mox-mox/solar/vreg5.pdf

## WEBENCH ® Design Report

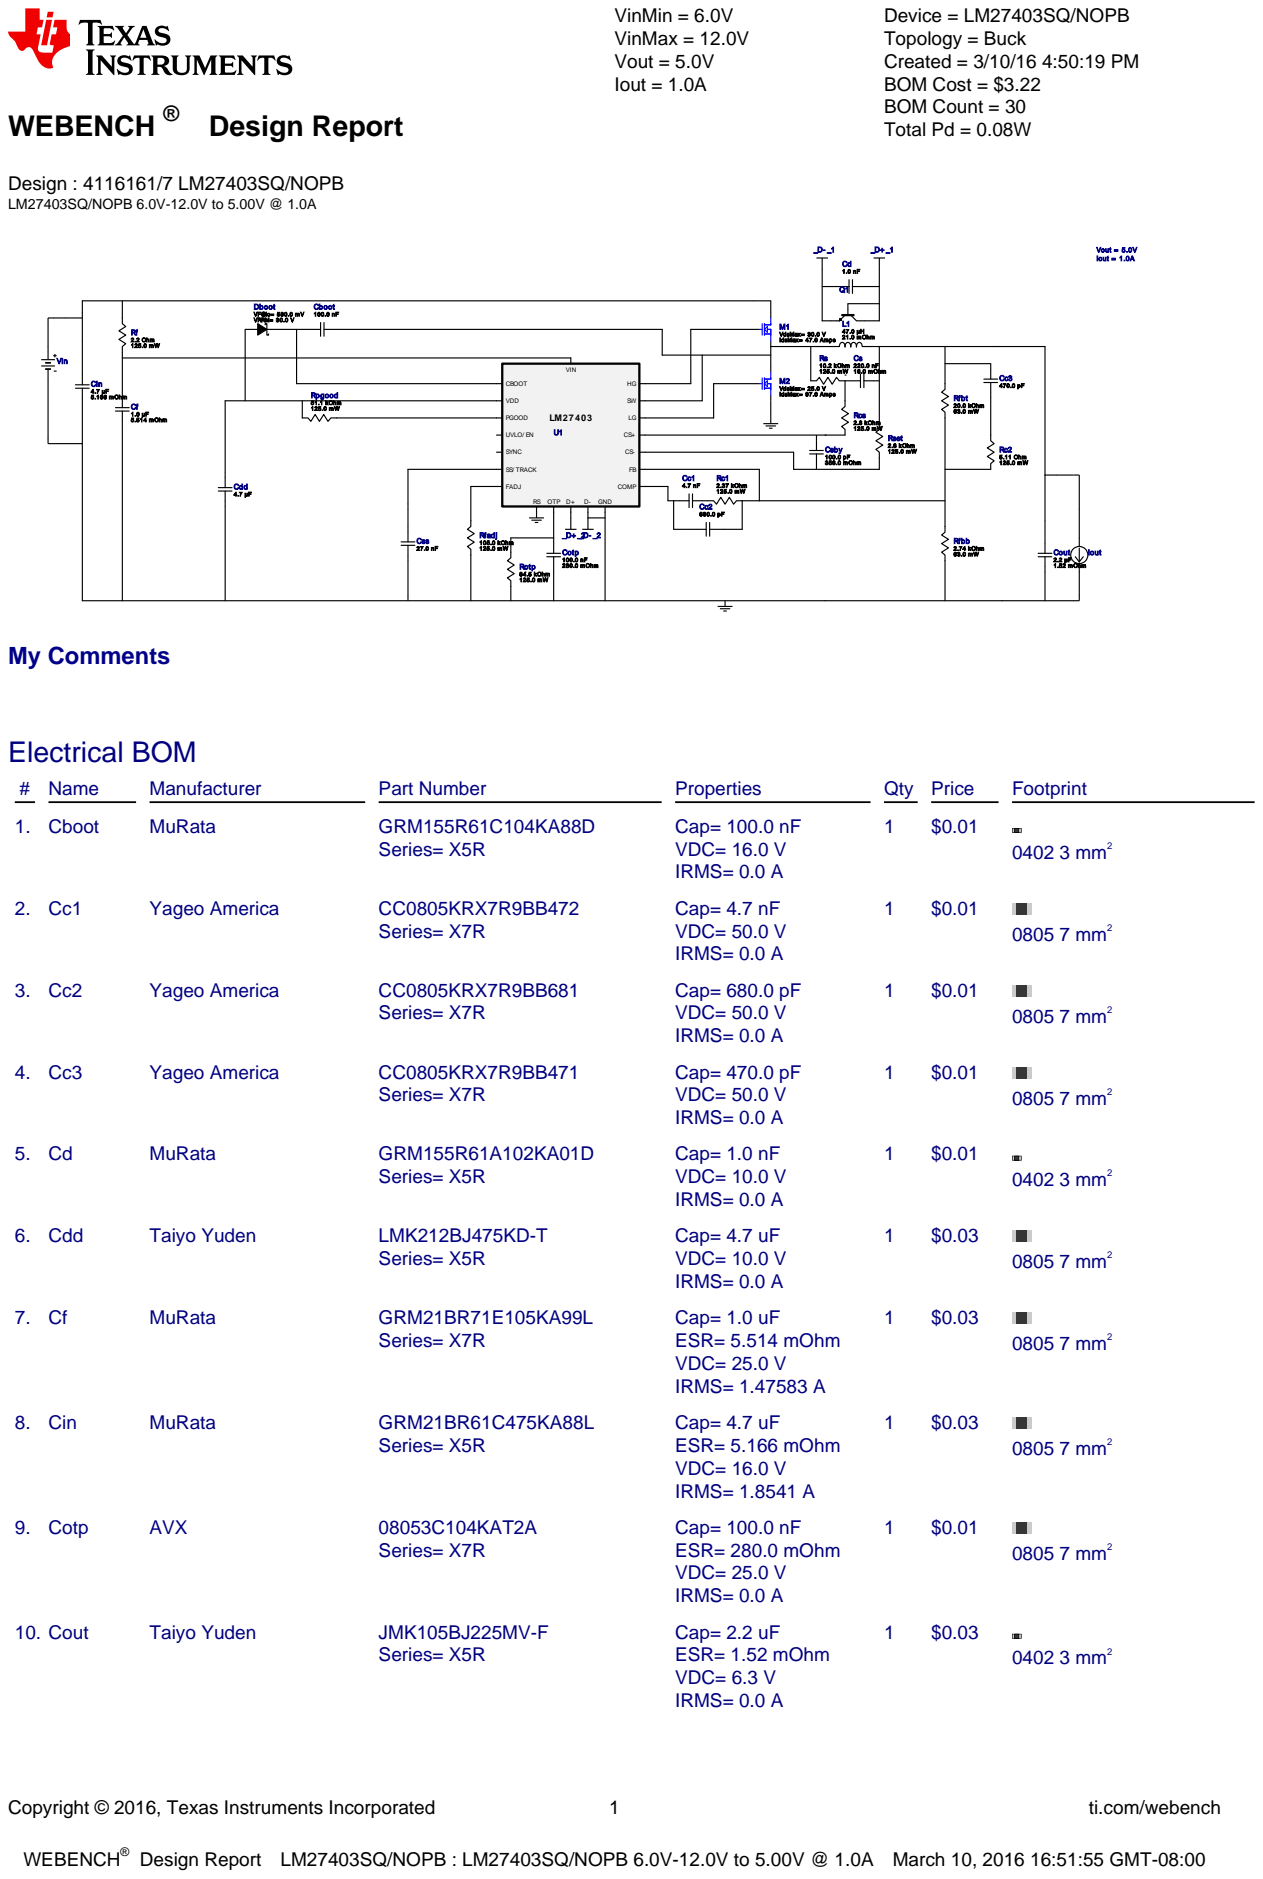
[picture p56: page 1]
Copyright © 2016, Texas Instruments Incorporated; ti.com/webench; WEBENCH®; Design : 4116161/7 LM27403SQ/NOPB LM27403SQ/NOPB 6.0V-12.0V to 5.00V @ 1.0A; VinMin = 6.0V VinMax = 12.0V Vout = 5.0V Iout = 1.0A; Device = LM27403SQ/NOPB Topology = Buck Created = 3/10/16 4:50:19 PM BOM Cost = $3.22 BOM Count = 30 Total Pd = 0.08W; Cboot 100.0 nF; Cdd 4.7 µF; 5.514 mOhm; Cin 4.7 µF 5.166 mOhm; Cotp 100.0 nF 280.0 mOhm; Cout 2.2 µF; 1.52 mOhm; Cs 220.0 nF 16.0 mOhm; Csby 100.0 pF 356.0 mOhm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

Dboot VF@Io= 580.0 mV

Design Report LM27403SQ/NOPB : LM27403SQ/NOPB 6.0V-12.0V to 5.00V @ 1.0A March 10, 2016 16:51:55 GMT-08:00

Design

Copyright © 2016, Texas Instruments Incorporated | 2 | ti.com/webench
# Name | Manufacturer | Part Number | Properties | Qty Price | Footprint

11. Cs | AVX | 0805YC224KAT2A (http://www.avx.com/docs/masterpubs/smccp.pdf) Series= X7R | Cap= 220.0 nF ESR= 16.0 mOhm VDC= 16.0 V IRMS= 0.0 A
1 | $0.03
| | | | | 0805 7 mm²
12. Csby | AVX | 08055A101JAT2A (http://www.avx.com/docs/masterpubs/smccp.pdf) Series= C0G/NP0

Cap= 100.0 pF
ESR= 356.0 mOhm
VDC= 50.0 V
IRMS= 0.0 A

1 $0.01
0805 7 mm²
13. Css | MuRata | GRM155R61C273KA01D (http://search.murata.co.jp/Ceramy/PnsearchViewAction.do) Series= X5R | Cap= 27.0 nF VDC= 16.0 V IRMS= 0.0 A
1 | $0.01
0402 3 mm²
14. Dboot | Diodes Inc. | SBR0230T5-7-F (http://www.diodes.com/datasheets/sbr/SBR0230T5.pdf) | VF@Io= 580.0 mV VRRM= 30.0 V
1 | $0.10
SOD-523 5 mm²
15. L1 | Coilcraft | SER1390-473MLB (http://www.coilcraft.com/pdfs/ser1390.pdf) | L= 47.0 µH DCR= 21.0 mOhm
1 | $0.95

SER1390 240 mm²
16. M1 | Texas Instruments | CSD17308Q3 (http://www.ti.com/lit/ds/symlink/csd17308q3.pdf) | VdsMax= 30.0 V IdsMax= 47.0 Amps | 1 | $0.34

TRANS_NexFET_Q3 18
mm²
17. M2 | Texas Instruments | CSD16322Q5C (http://focus.ti.com/lit/ds/symlink/csd16322q5c.pdf) | VdsMax= 25.0 V IdsMax= 97.0 Amps | 1 | $0.50

TRANS_NexFET_Q5C 56
mm²
18. Q1 | Diodes Inc. | MMBT3904T (http://www.diodes.com/datasheets/ds30270.pdf) | Bipolar Transistor | 1 | $0.04
SOT-523 7 mm²
19. Rc1 | Panasonic | ERJ-6ENF2371V (http://www.panasonic.com/industrial/components/pdf/AOA0000CE2.pdf) Series= ERJ-6E | Res= 2.37 kOhm Power= 125.0 mW Tolerance= 1.0% | 1 | $0.01
0805 7 mm²
20. Rc2 | Vishay-Dale | CRCW08055R11FKEA (http://www.vishay.com/docs/20035/dcrcwe3.pdf) Series= CRCW..e3 | Res= 5.11 Ohm Power= 125.0 mW Tolerance= 1.0% | 1 | $0.01
0805 7 mm²
21. Rcs | Panasonic | ERJ-6ENF2801V (http://www.panasonic.com/industrial/components/pdf/AOA0000CE2.pdf) Series= ERJ-6E | Res= 2.8 kOhm Power= 125.0 mW Tolerance= 1.0% | 1 | $0.01
0805 7 mm²
22. Rf | Yageo America | RC0805FR-072R2L (http://www.yageo.com/documents/recent/PYu%2DRC0805%5F51%5FRoHS%5FL%5F6.pdf) Series= ? | Res= 2.2 Ohm Power= 125.0 mW Tolerance= 1.0% | 1 | $0.01
0805 7 mm²
23. Rfadj | Panasonic | ERJ-6ENF1053V (http://www.panasonic.com/industrial/components/pdf/AOA0000CE2.pdf) Series= ERJ-6E | Res= 105.0 kOhm Power= 125.0 mW Tolerance= 1.0% | 1 | $0.01
0805 7 mm²
24. Rfbb | Vishay-Dale | CRCW04022K74FKED (http://www.vishay.com/docs/20035/dcrcwe3.pdf) Series= CRCW..e3 | Res= 2.74 kOhm Power= 63.0 mW Tolerance= 1.0% | 1 | $0.01
0402 3 mm²
25. Rfbt | Vishay-Dale | CRCW040220K0FKED (http://www.vishay.com/docs/20035/dcrcwe3.pdf) Series= CRCW..e3 | Res= 20.0 kOhm Power= 63.0 mW Tolerance= 1.0% | 1 | $0.01
0402 3 mm²
26. Rotp | Panasonic | ERJ-6ENF8452V (http://www.panasonic.com/industrial/components/pdf/AOA0000CE2.pdf) Series= ERJ-6E | Res= 84.5 kOhm Power= 125.0 mW Tolerance= 1.0% | 1 | $0.01
0805 7 mm²
27. Rpgood | Panasonic | ERJ-6ENF5112V (http://www.panasonic.com/industrial/components/pdf/AOA0000CE2.pdf) Series= ERJ-6E | Res= 51.1 kOhm Power= 125.0 mW Tolerance= 1.0% | 1 | $0.01
0805 7 mm²
28. Rs | Panasonic | ERJ-6ENF1022V (http://www.panasonic.com/industrial/components/pdf/AOA0000CE2.pdf) Series= ERJ-6E | Res= 10.2 kOhm Power= 125.0 mW Tolerance= 1.0% | 1 | $0.01
0805 7 mm²

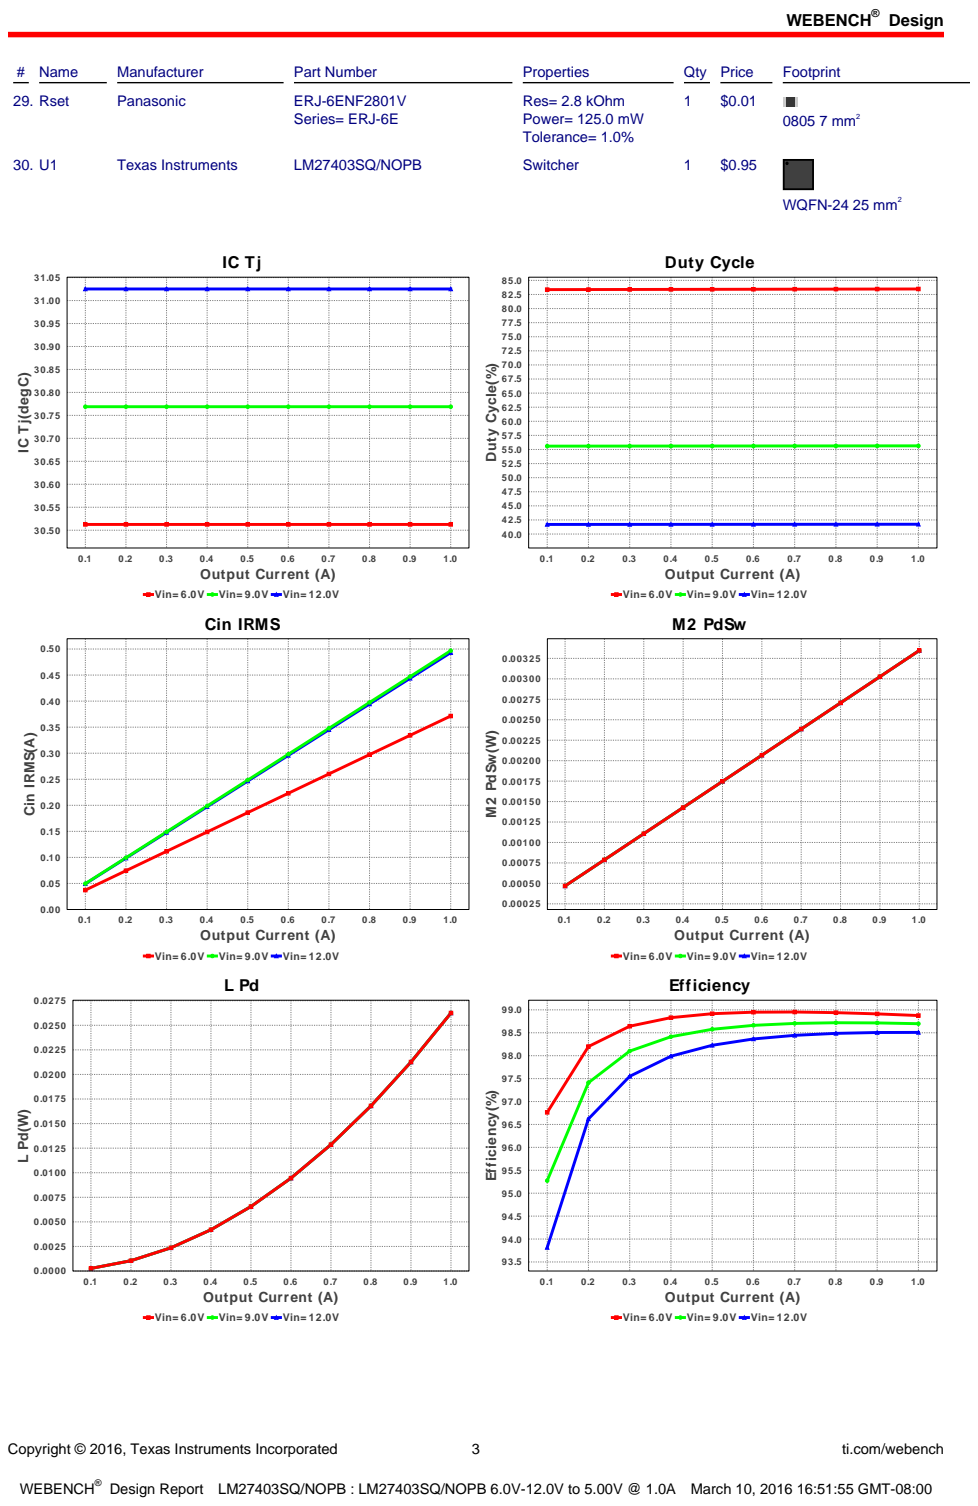
[picture p57: page 3]
Copyright © 2016, Texas Instruments Incorporated; ti.com/webench; # Name; Manufacturer; Part Number; Properties; Qty Price; Footprint; 29. Rset; Panasonic; ERJ-6ENF2801V; Series= ERJ-6E; Res= 2.8 kOhm Power= 125.0 mW Tolerance= 1.0%; 0805 7 mm²; Texas Instruments; LM27403SQ/NOPB; Switcher; WQFN-24 25 mm²; 1.0 Output Current (A); Duty Cycle; Duty Cycle(%); Cin IRMS(A); M2 PdSw(W); Efficiency(%)

IC Tj(degC)

Vin= 6.0V Vin= 9.0V Vin= 12.0V
Cin IRMS

M2 PdSw

Efficiency

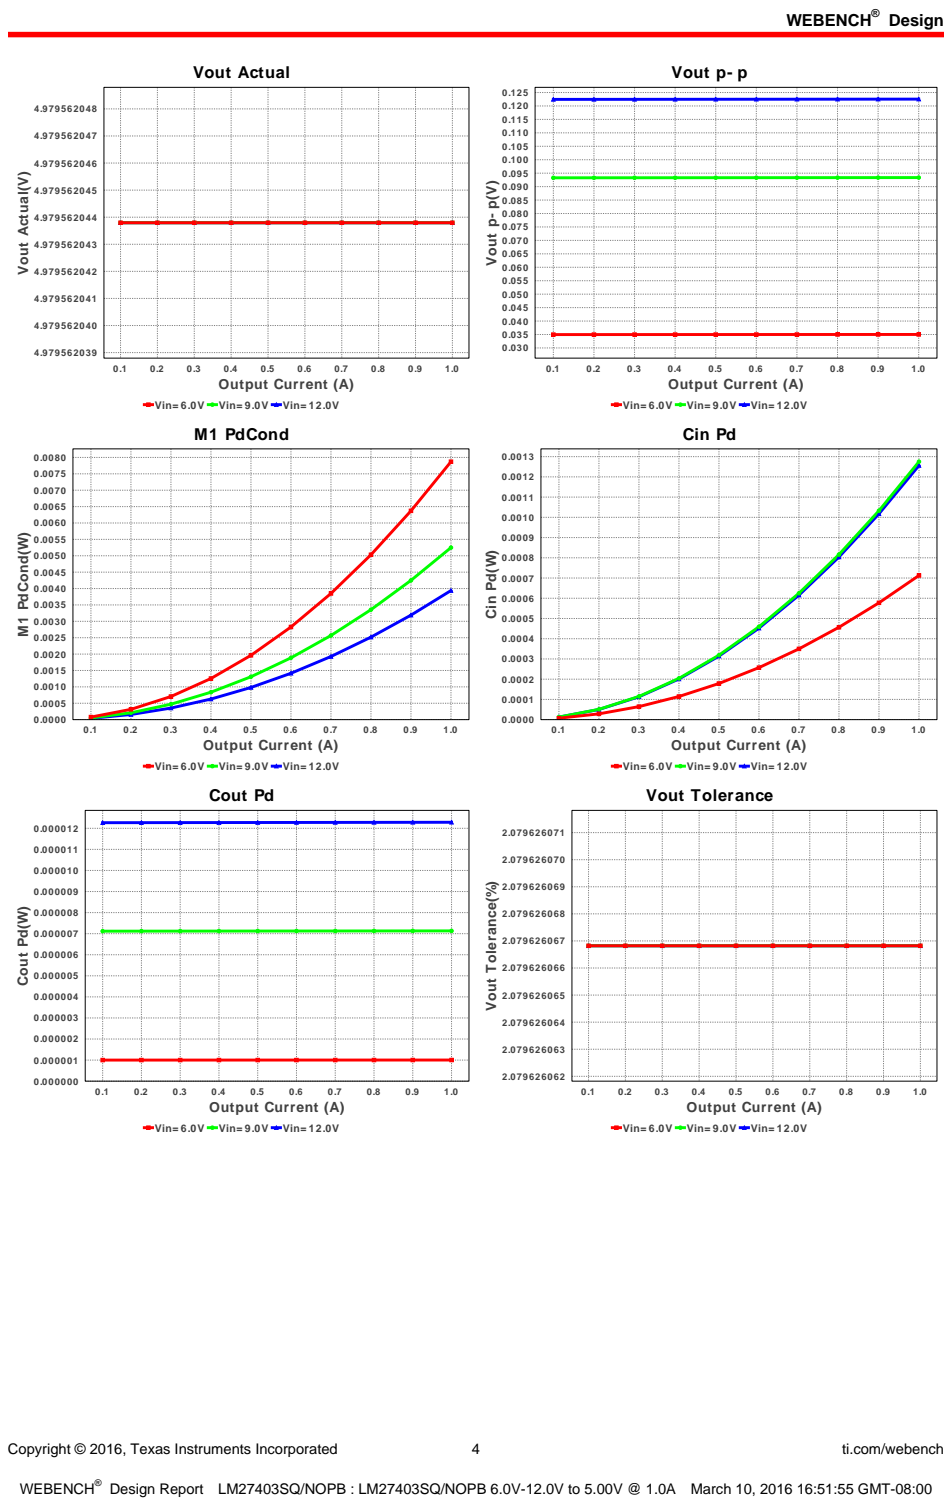
[picture p58: page 4]
Copyright © 2016, Texas Instruments Incorporated; ti.com/webench; Vout Actual; 1.0 Output Current (A); Vout Actual(V); Vout p- p; Vout p- p(V); M1 PdCond(W); Cin Pd; Cin Pd(W); Cout Pd(W); Vout Tolerance(%)

Vin= 6.0V Vin= 9.0V Vin= 12.0V
M1 PdCond

Cout Pd

Vout Tolerance

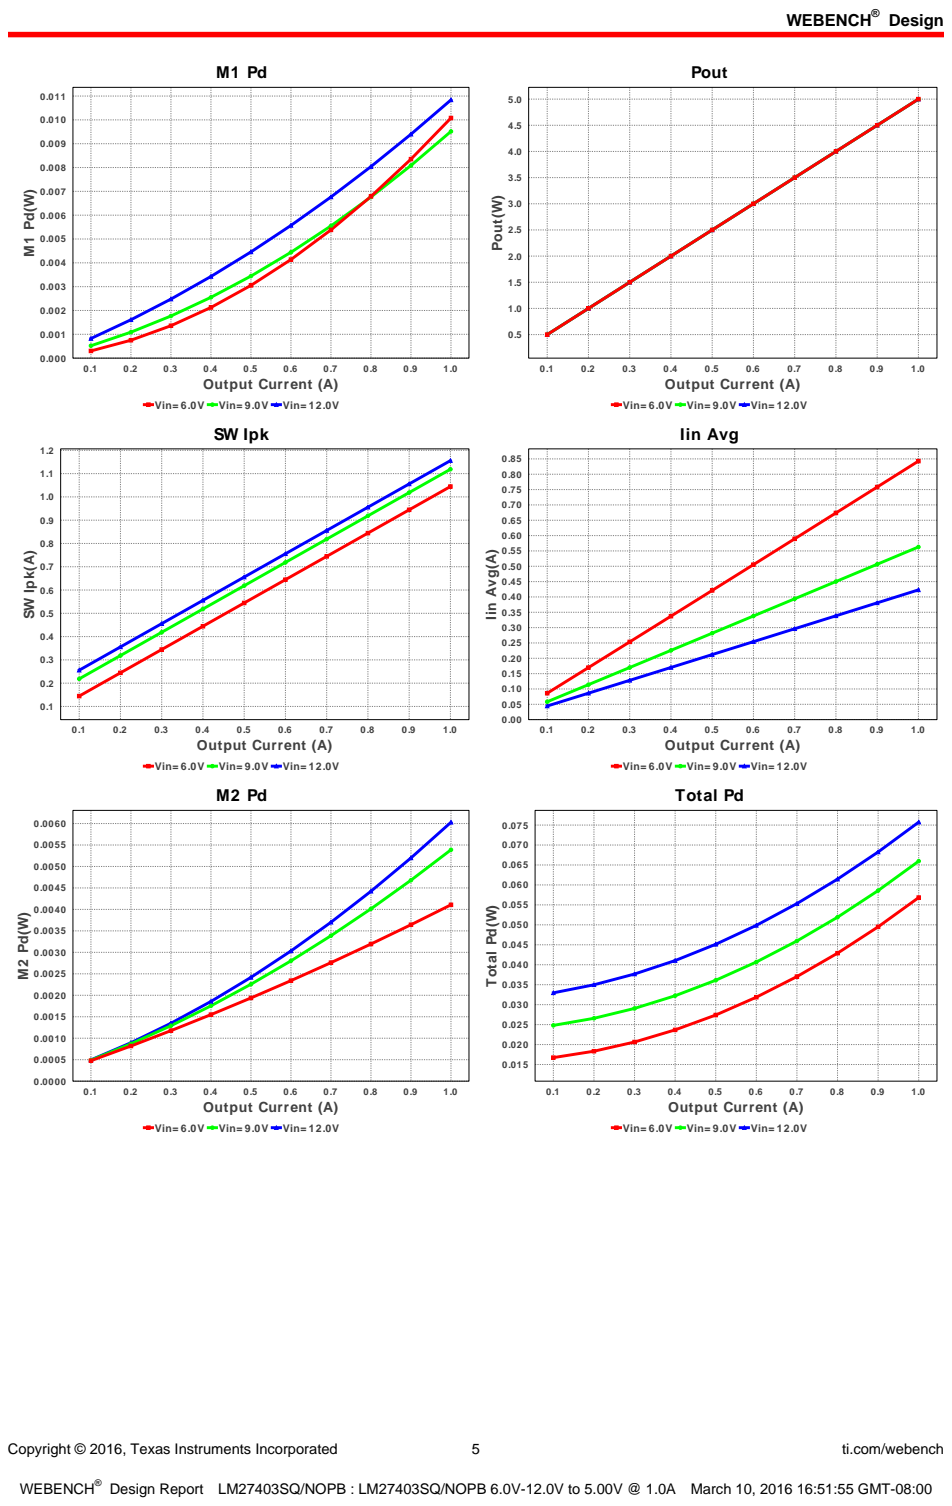
[picture p59: page 5]
Copyright © 2016, Texas Instruments Incorporated; ti.com/webench; 1.0 Output Current (A); Pout; Pout(W); SW Ipk; SW Ipk(A); Iin Avg(A); Total Pd(W)

Vin= 6.0V Vin= 9.0V Vin= 12.0V

Iin Avg

Total Pd

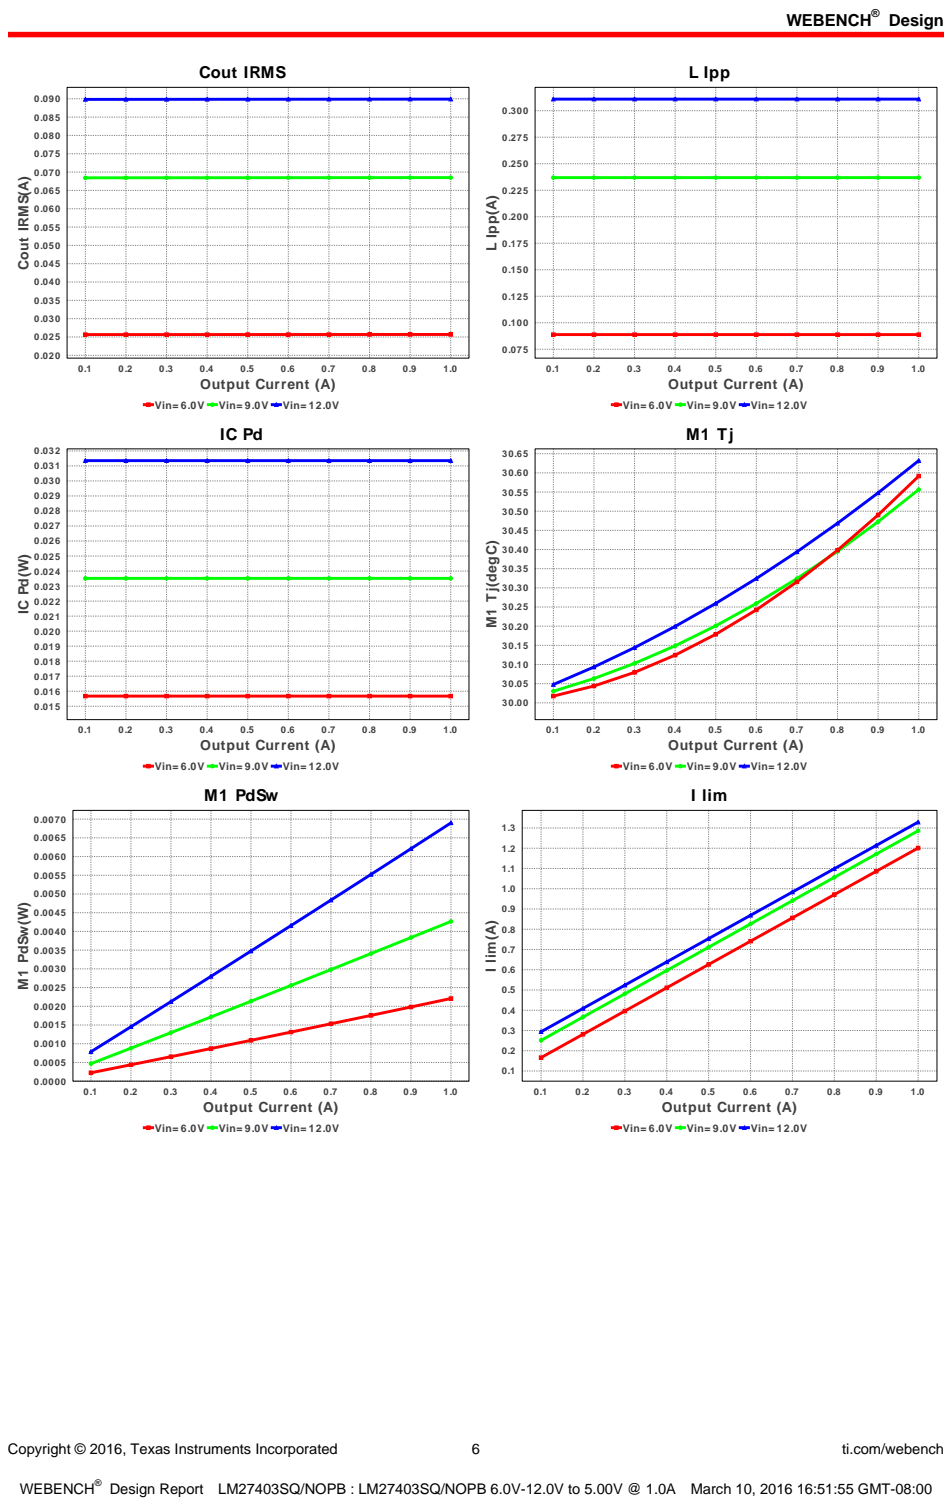
[picture p60: page 6]
Copyright © 2016, Texas Instruments Incorporated; ti.com/webench; Cout IRMS; 1.0 Output Current (A); Cout IRMS(A); L Ipp; L Ipp(A); M1 Tj(degC); M1 PdSw(W); I lim; I lim(A)

Vin= 6.0V Vin= 9.0V Vin= 12.0V

M1 PdSw

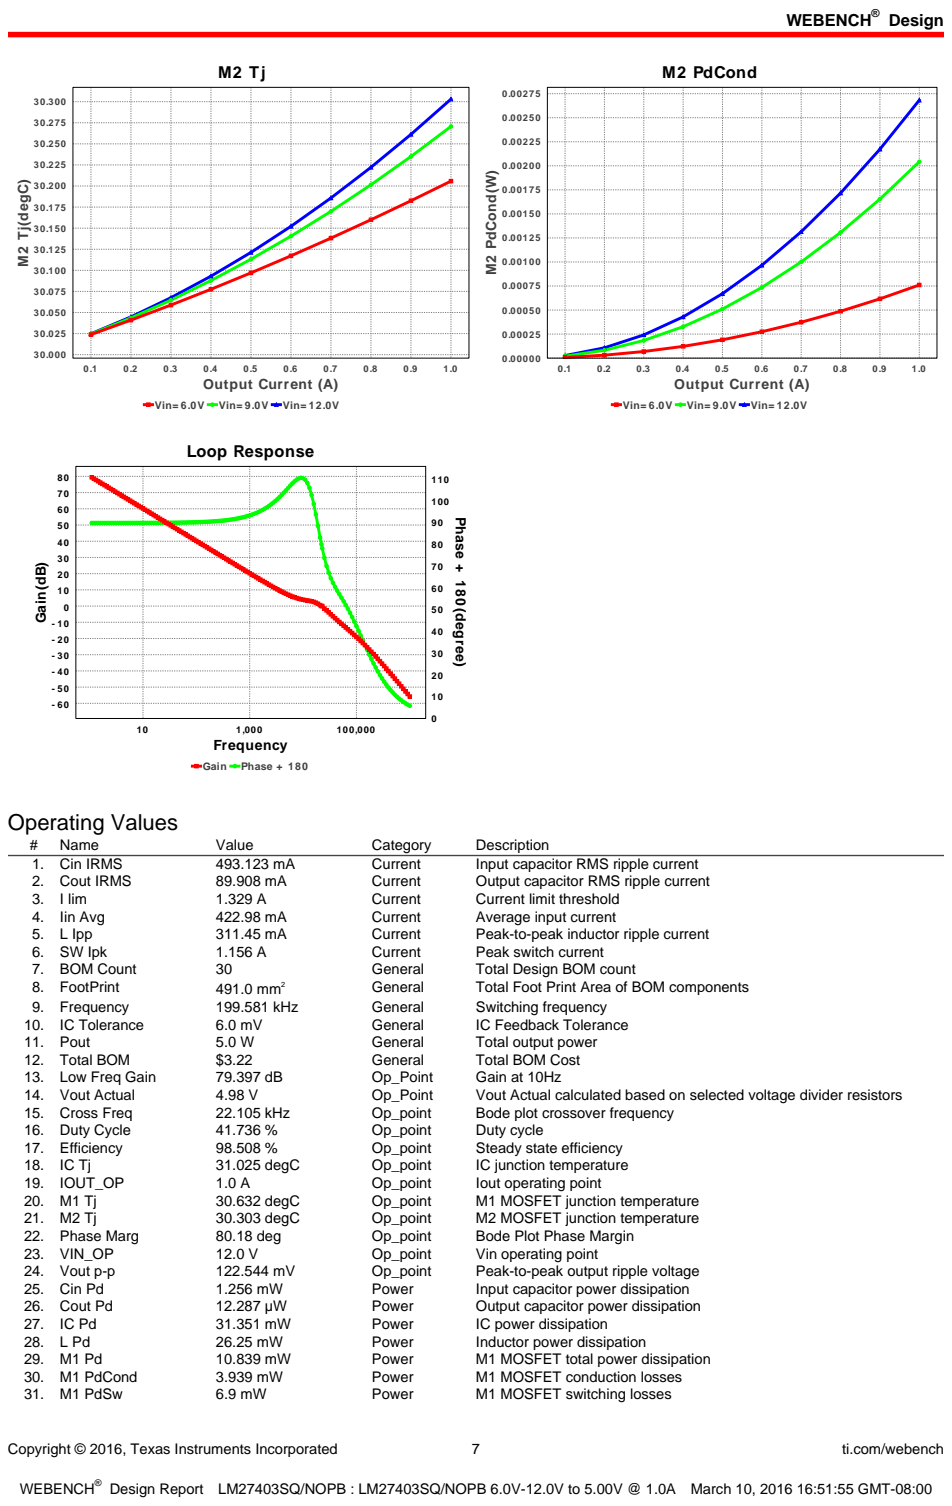
[picture p61: page 7]
Copyright © 2016, Texas Instruments Incorporated; ti.com/webench; 1.0 Output Current (A); M2 Tj(degC); M2 PdCond; M2 PdCond(W); Loop Response; Gain Phase + 180; 100,000 Frequency; Gain(dB); Phase + 180(degree); Operating Values; Name; Value; Category; Description; 1. Cin IRMS; Current; Input capacitor RMS ripple current; 2. Cout IRMS; Output capacitor RMS ripple current; 3. I lim; Current limit threshold; 4. Iin Avg; Average input current; 5. L Ipp; Peak-to-peak inductor ripple current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

Vin= 6.0V Vin= 9.0V Vin= 12.0V

Copyright © 2016, Texas Instruments Incorporated | 8 | ti.com/webench
# | Name | Value | Category | Description

32. M2 Pd | 6.029 mW | Power | M2 MOSFET total power dissipation
33. M2 PdCond | 2.682 mW | Power | M2 MOSFET conduction losses
34. M2 PdSw | 3.347 mW | Power | M2 MOSFET switching losses
35. Total Pd | 75.73 mW | Power | Total Power Dissipation
36. Vout Tolerance | 2.08 % | Vout Tolerance based on IC Tolerance and voltage divider resistors if
| | | | applicable

## Design Inputs

# | Name | Value | Description

1. Iout | 1.0 | Maximum Output Current
2. VinMax | 12.0 | Maximum input voltage
3. VinMin | 6.0 | Minimum input voltage
4. Vout | 5.0 | Output Voltage
5. base_pn | LM27403 | Base Product Number
6. source | DC | Input Source Type
7. Ta | 30.0 | Ambient temperature

## Design Assistance

1. Tip: LM27403 High Current PCB Layout Design Guidance For higher current designs, please take care in designing the PCB layout. Consider good thermal management practices and proper routing of traces. Please see the following for more guidelines. Best Layout Practices for Switching Power Supplies http://sva.ti.com/assets/en/appnotes/national_power_designer114.pdf SIMPLE SWITCHER Layout Guidelines http://www.ti.com/lit/an/snva054c/snva054c.pdf Thermal Design by Insight, not Hindsight http://www.ti.com/lit/an/snva419c/snva419c.pdf
2. General Description: The LM27403 is a synchronous voltage mode buck controller with inductor DCR current sense capability. Sensing the inductor current eliminates the need to add resistive powertrain elements which increases overall efficiency and allows for accurate continuous current limit sensing. A 0.6V +/-1% voltage reference permits high accuracy and low voltage capability at the output. An operating voltage range of 3V to 20V makes the LM27403 suitable for a large variety of input rails. The LM27403 voltage mode control loop incorporates input voltage feed-forward to maintain stability throughout the entire input voltage range. The switching frequency is adjustable from 200 kHz to 1.2 MHz allowing a flexible design space. A power good indicator provides power rail sequencing capability and output fault detection. Programmable external softstart capability limits inrush current and provides monotonic output control at startup. Other features include external tracking of other power supplies, integrated LDO bias supply, and synchronization capability.
3. LM27403 Product Folder : http://www.ti.com/product/LM27403 : contains the data sheet and other resources.

Texas Instruments' WEBENCH simulation tools attempt to recreate the performance of a substantially equivalent physical implementation
of the design. Simulations are created using Texas Instruments' published specifications as well as the published specifications of other device manufacturers. While Texas Instruments does update this information periodically, this information may not be current at the time the simulation is built. Texas Instruments does not warrant the accuracy or completeness of the specifications or any information contained therein. Texas Instruments does not warrant that any designs or recommended parts will meet the specifications you entered, will be suitable for your application or fit for any particular purpose, or will operate as shown in the simulation in a physical implementation. Texas Instruments does not warrant that the designs are production worthy.
You should completely validate and test your design implementation to confirm the system functionality for your application prior to production.
Use of Texas Instruments' WEBENCH simulation tools is subject to Texas Instruments' Site Terms and Conditions of Use. (http://www.ti.com/corp/docs/legal/termsofuse.shtml) Prototype boards based on WEBENCH created designs are provided AS IS without warranty of any kind for evaluation and testing purposes and are subject to the terms of the Evaluation License Agreement. (http://www.ti.com/corp/docs/legal/termsofuse_estore.shtml)
